JeffOwOSun/cosmotyl/docs/img/v3_hull_viewer.png

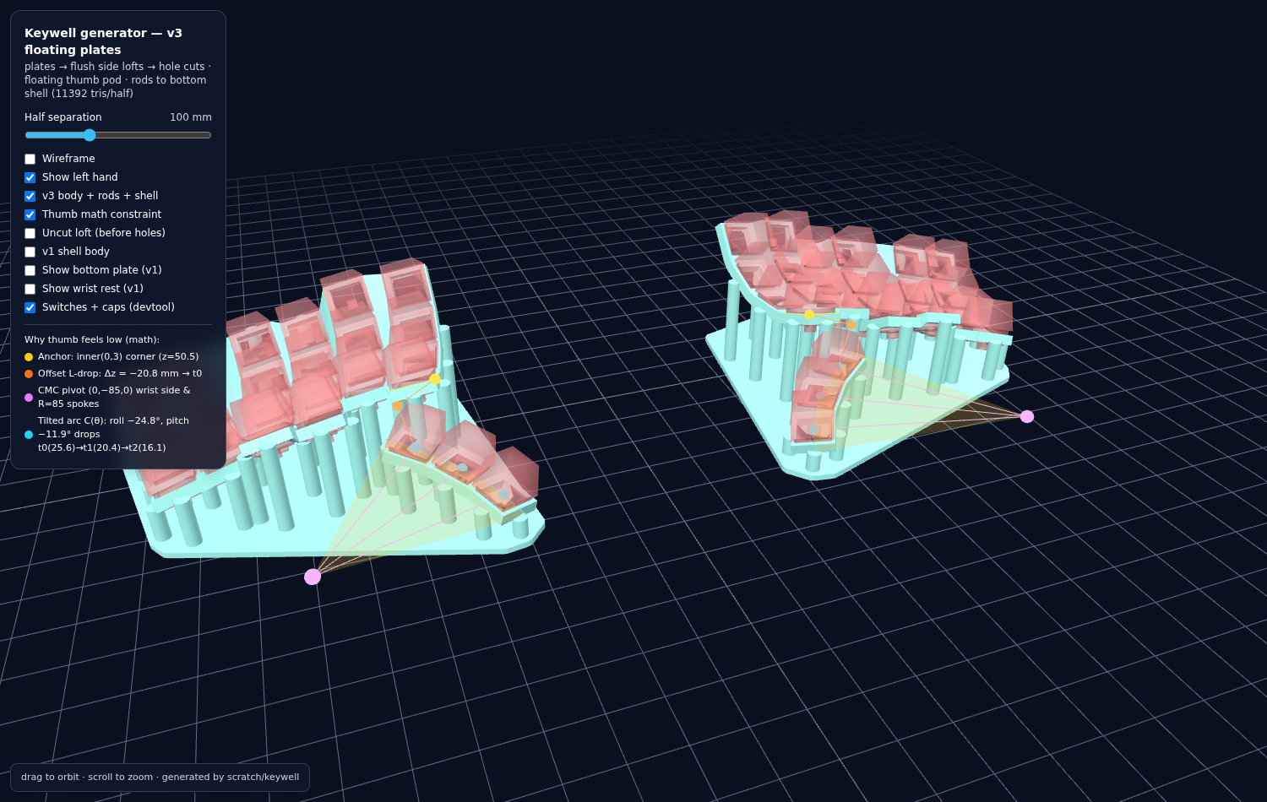
docs/img/v3_hull_viewer.png
